rduart/TelsaCoilWinder/EasyEDA/PCB_PCB_DVR8825V5_2024-05-20.png

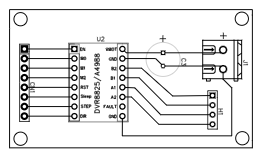
EasyEDA/PCB_PCB_DVR8825V5_2024-05-20.png
