rduart/TelsaCoilWinder/Images/20240512_073756.jpg

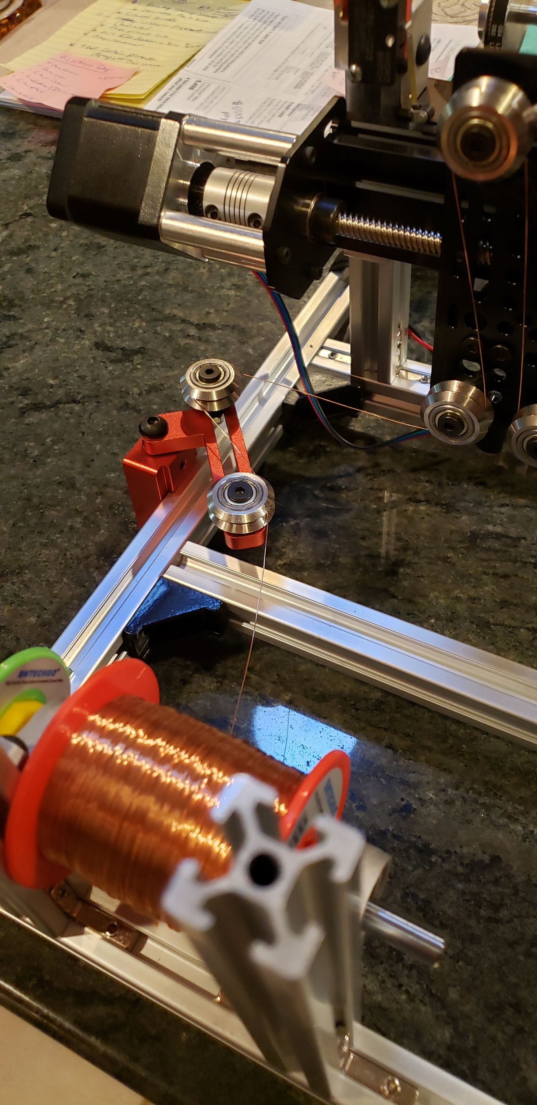
Images/20240512_073756.jpg
