rduart/TelsaCoilWinder/Images/20240512_073829.jpg

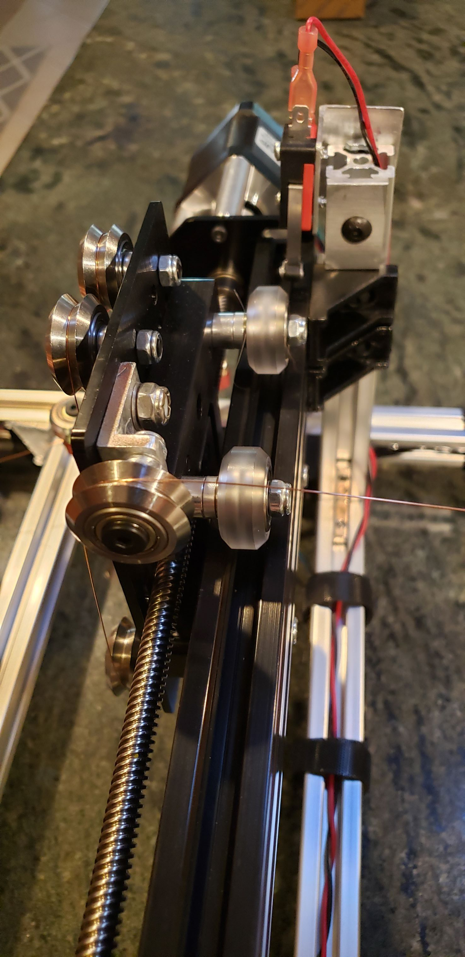
Images/20240512_073829.jpg
