rduart/TelsaCoilWinder/Images/20240512_082015.jpg

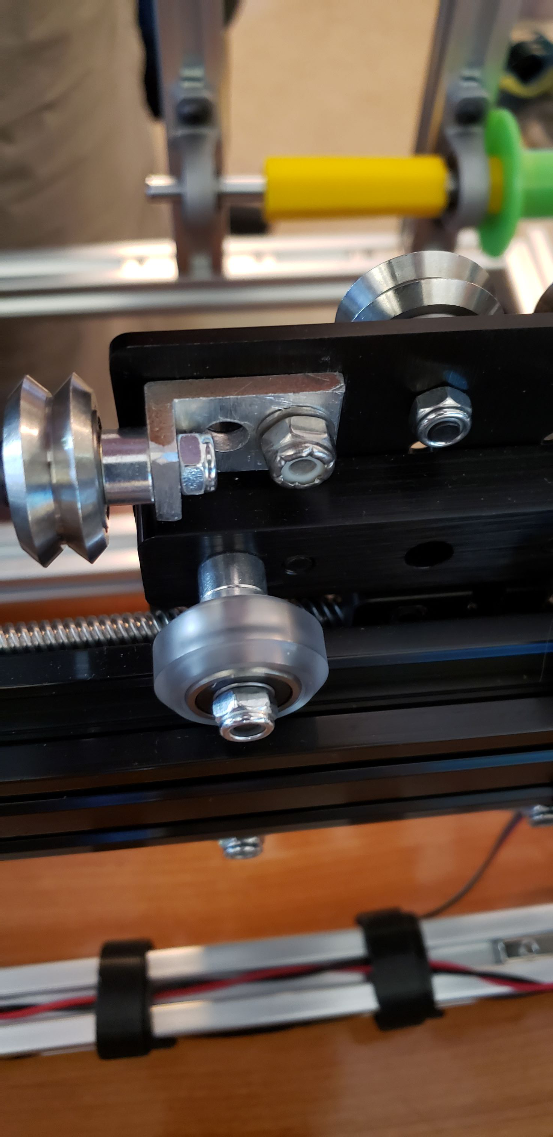
Images/20240512_082015.jpg
