rduart/TelsaCoilWinder/Images/20240512_082021.jpg

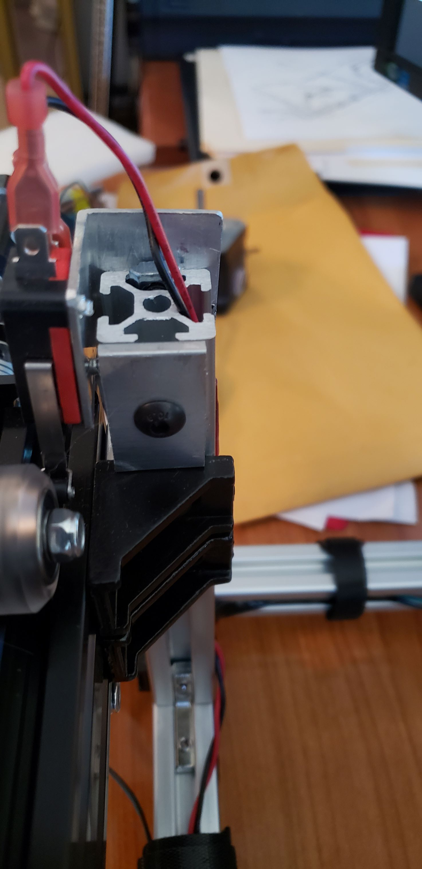
Images/20240512_082021.jpg
