rduart/TelsaCoilWinder/Images/20240512_082038.jpg

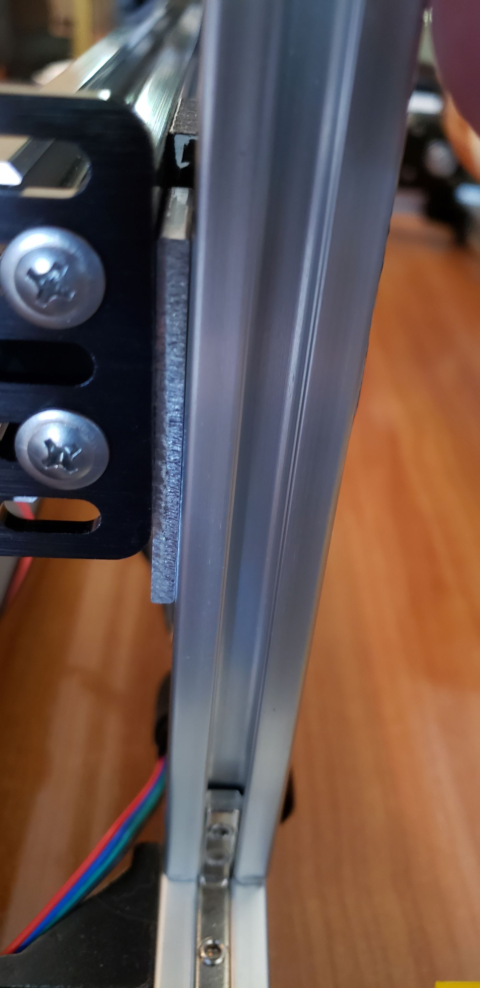
Images/20240512_082038.jpg
