rduart/TelsaCoilWinder/Images/20240512_082049.jpg

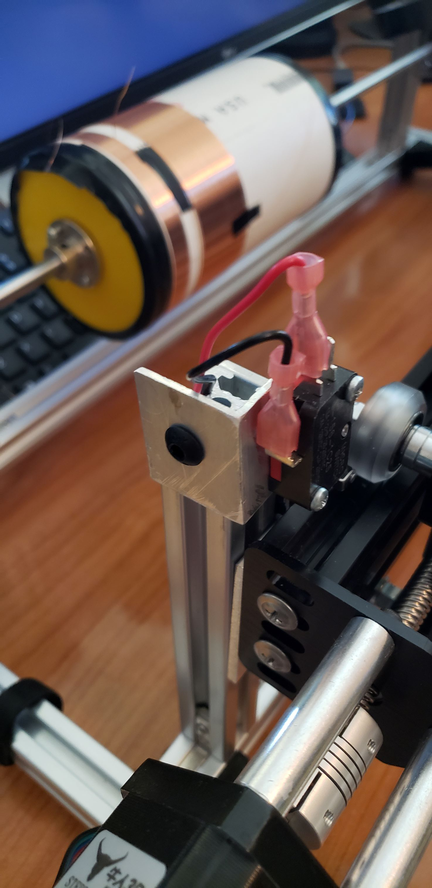
Images/20240512_082049.jpg
