rduart/TelsaCoilWinder/Images/Awg26Wire.jpg

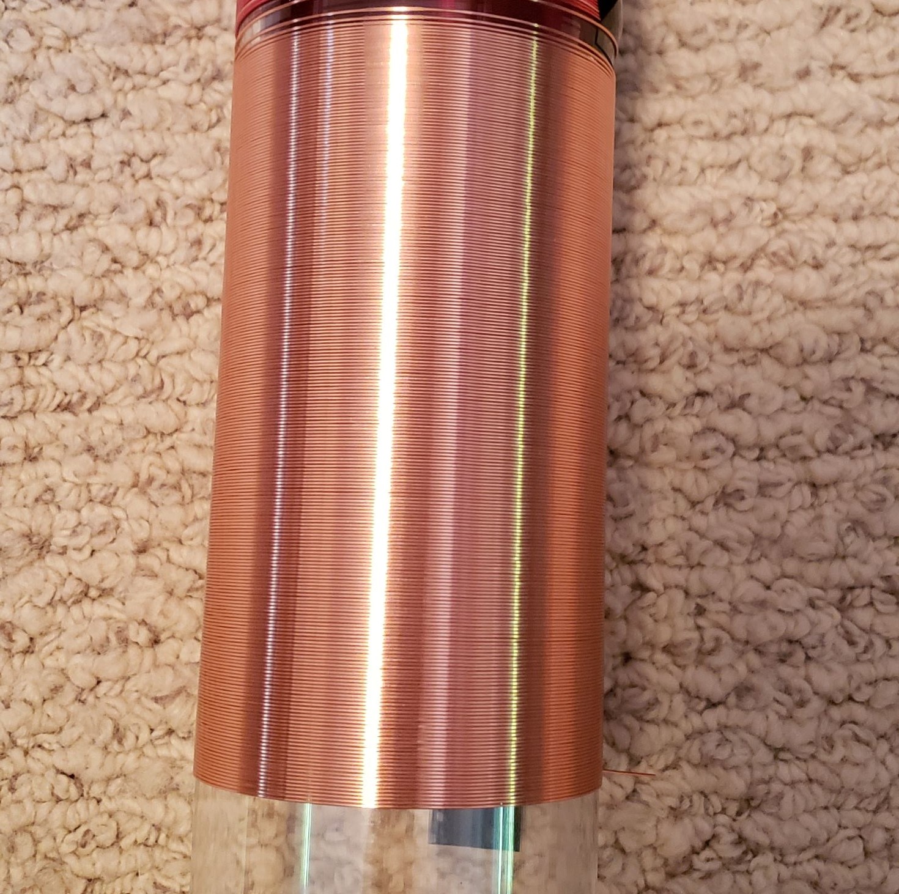
Images/Awg26Wire.jpg
