rduart/TelsaCoilWinder/Images/Awg28Wire.jpg

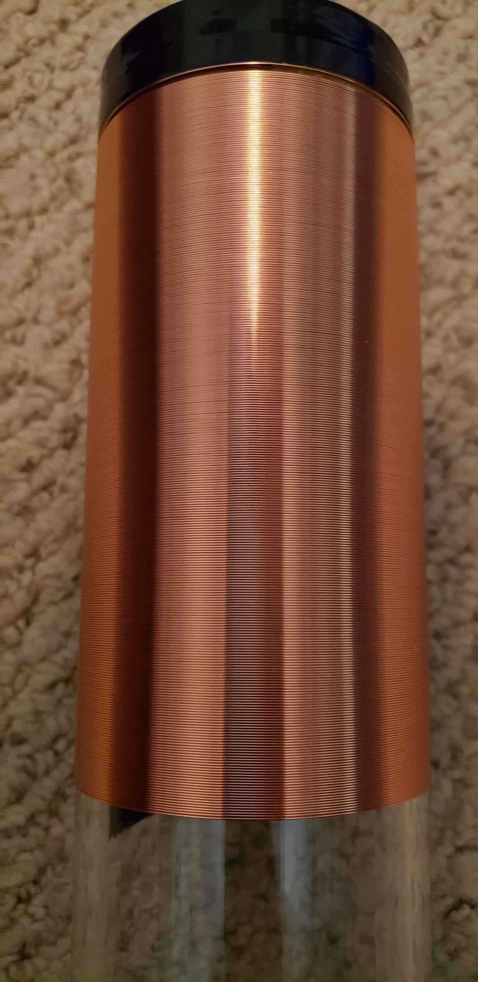
Images/Awg28Wire.jpg
