rduart/TelsaCoilWinder/Images/Awg36Wire.jpg

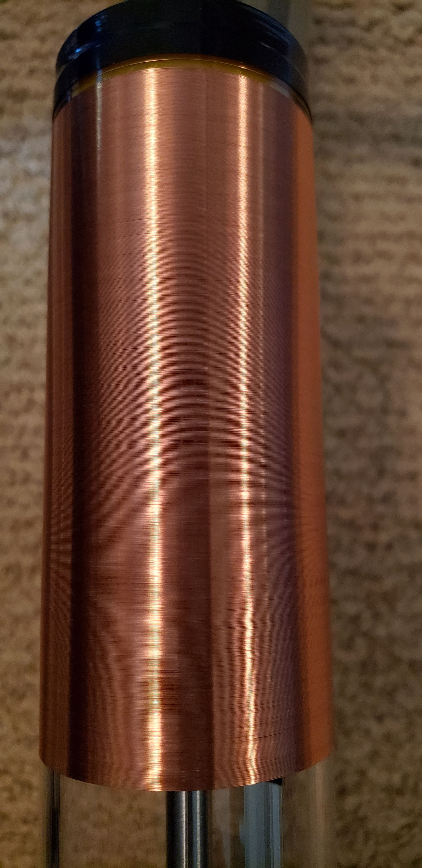
Images/Awg36Wire.jpg
