rduart/TelsaCoilWinder/Images/Coil2.jpg

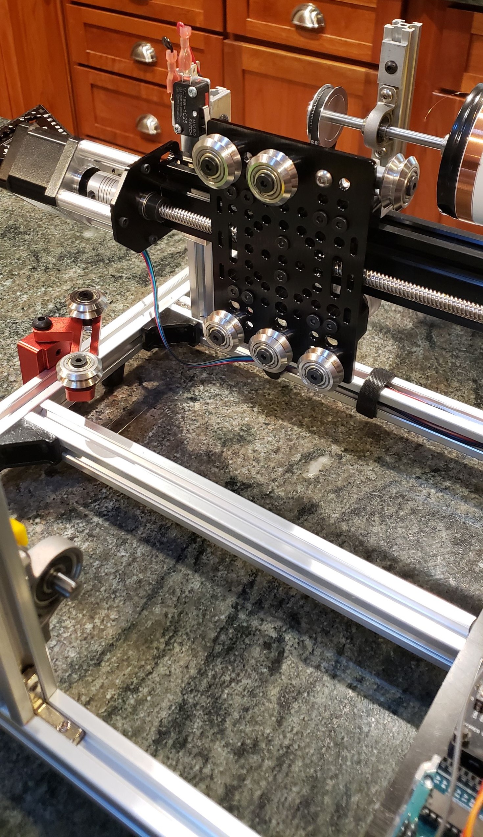
Images/Coil2.jpg
