rduart/TelsaCoilWinder/Images/page0.jpg

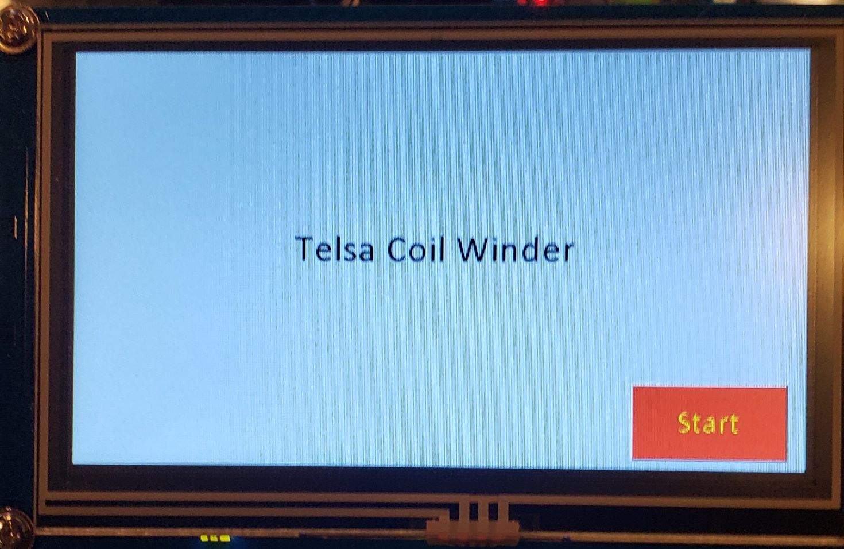
Images/page0.jpg
