rduart/TelsaCoilWinder/Images/page1.jpg

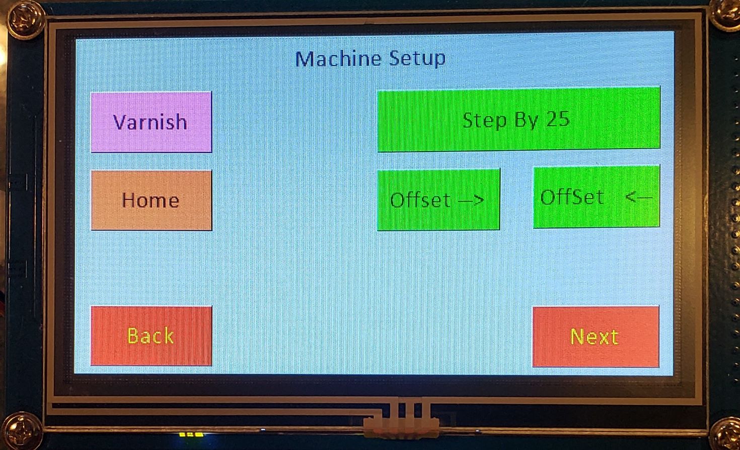
Images/page1.jpg
