rduart/TelsaCoilWinder/Images/page3.jpg

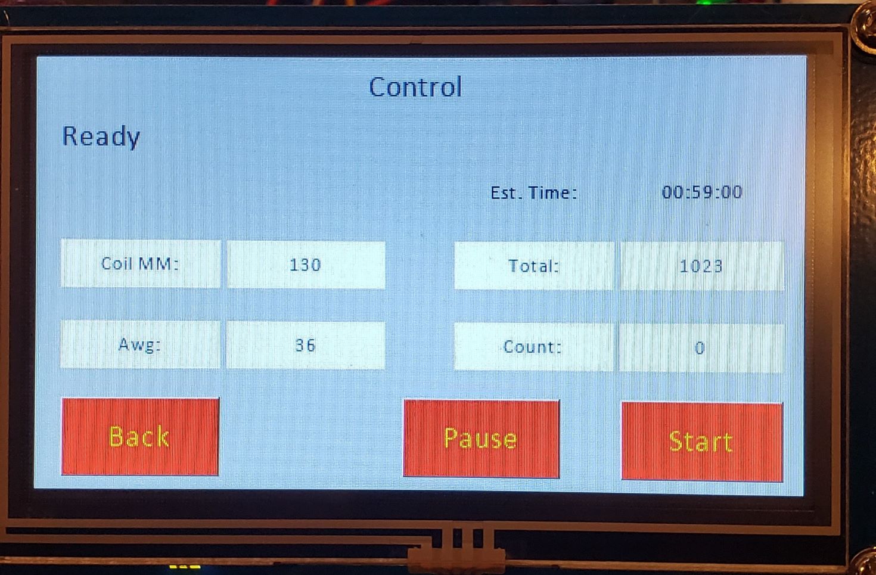
Images/page3.jpg
