rduart/TelsaCoilWinder/Images/Tension.jpg

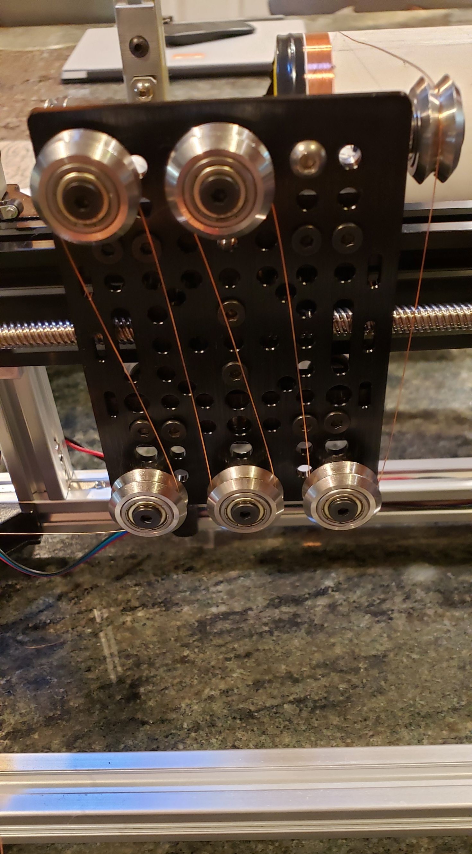
Images/Tension.jpg
