rduart/TelsaCoilWinder/Images/WindingAwg26.jpg

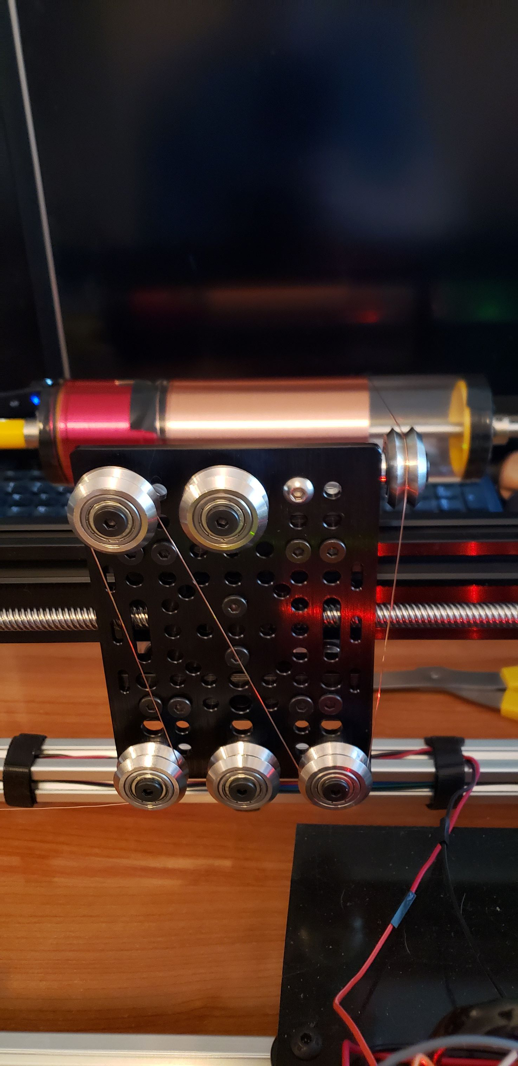
Images/WindingAwg26.jpg
